ninjaco1/Adaptive-Controller-Project/F/_EmbeddedPCB.0f97f602-2c7d-4791-9238-98ac81d9567d.png

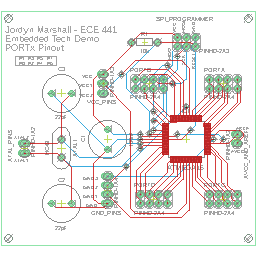
F/_EmbeddedPCB.0f97f602-2c7d-4791-9238-98ac81d9567d.png
