ninjaco1/Adaptive-Controller-Project/F/_EmbeddedPCB.33aa806d-3ddb-4efb-9624-6a5cfd5aa2a7.png

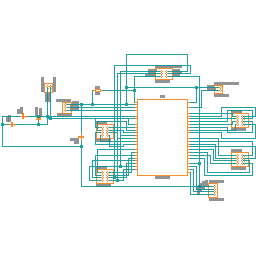
F/_EmbeddedPCB.33aa806d-3ddb-4efb-9624-6a5cfd5aa2a7.png
